Xinyuan-LilyGO/LilyGo-T-SIM7080G/examples/ModemFileUploadExample/image.png

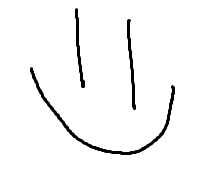
examples/ModemFileUploadExample/image.png
