Xinyuan-LilyGO/LilyGo-T-SIM7080G/examples/LoRaShield_LoRaTransmit/LoRaShield_LoRaTransmit.ino

/*
  RadioLib SX126x Transmit with Interrupts Example

  This example transmits LoRa packets with one second delays
  between them. Each packet contains up to 256 bytes
  of data, in the form of:
  - Arduino String
  - null-terminated char array (C-string)
  - arbitrary binary data (byte array)

  Other modules from SX126x family can also be used.

  For default module settings, see the wiki page
  https://github.com/jgromes/RadioLib/wiki/Default-configuration#sx126x---lora-modem

  For full API reference, see the GitHub Pages
  https://jgromes.github.io/RadioLib/
*/

//  * @note      This example is only available for SimShield

// include the library
#include <RadioLib.h>

#define SIMSHIELD_MOSI                      (11)
#define SIMSHIELD_MISO                      (13)
#define SIMSHIELD_SCK                       (12)
#define SIMSHIELD_SD_CS                     (21)
#define SIMSHIELD_RADIO_BUSY                (48)
#define SIMSHIELD_RADIO_CS                  (45)
#define SIMSHIELD_RADIO_IRQ                 (8)
#define SIMSHIELD_RADIO_RST                 (47)

SX1262 radio = new Module(SIMSHIELD_RADIO_CS, SIMSHIELD_RADIO_IRQ, SIMSHIELD_RADIO_RST, SIMSHIELD_RADIO_BUSY);

// save transmission state between loops
int transmissionState = RADIOLIB_ERR_NONE;

// flag to indicate that a packet was sent
volatile bool transmittedFlag = false;

// this function is called when a complete packet
// is transmitted by the module
// IMPORTANT: this function MUST be 'void' type
//            and MUST NOT have any arguments!
ICACHE_RAM_ATTR void setFlag(void)
{
    // we sent a packet, set the flag
    transmittedFlag = true;
}

void setup()
{
    Serial.begin(115200);

    //Pull spi devices cs to high
    pinMode(SIMSHIELD_SD_CS, OUTPUT);
    pinMode(SIMSHIELD_RADIO_CS, OUTPUT);

    digitalWrite(SIMSHIELD_SD_CS, HIGH);
    digitalWrite(SIMSHIELD_RADIO_CS, HIGH);

    SPI.begin(SIMSHIELD_SCK, SIMSHIELD_MISO, SIMSHIELD_MOSI);

    // initialize SX1262 with default settings
    Serial.print(F("[SX1262] Initializing ... "));
    int state = radio.begin(868.0);
    if (state == RADIOLIB_ERR_NONE) {
        Serial.println(F("success!"));
    } else {
        Serial.print(F("failed, code "));
        Serial.println(state);
        while (true) {
            delay(10);
        }
    }

    // set the function that will be called
    // when packet transmission is finished
    radio.setPacketSentAction(setFlag);

    // start transmitting the first packet
    Serial.print(F("[SX1262] Sending first packet ... "));

    // you can transmit C-string or Arduino string up to
    // 256 characters long
    transmissionState = radio.startTransmit("Hello World!");

    // you can also transmit byte array up to 256 bytes long
    /*
      byte byteArr[] = {0x01, 0x23, 0x45, 0x67,
                        0x89, 0xAB, 0xCD, 0xEF};
      state = radio.startTransmit(byteArr, 8);
    */
}

// counter to keep track of transmitted packets
int count = 0;

void loop()
{
    // check if the previous transmission finished
    if (transmittedFlag) {
        // reset flag
        transmittedFlag = false;

        if (transmissionState == RADIOLIB_ERR_NONE) {
            // packet was successfully sent
            Serial.println(F("transmission finished!"));

            // NOTE: when using interrupt-driven transmit method,
            //       it is not possible to automatically measure
            //       transmission data rate using getDataRate()

        } else {
            Serial.print(F("failed, code "));
            Serial.println(transmissionState);

        }

        // clean up after transmission is finished
        // this will ensure transmitter is disabled,
        // RF switch is powered down etc.
        radio.finishTransmit();

        // wait a second before transmitting again
        delay(1000);

        // send another one
        Serial.print(F("[SX1262] Sending another packet ... "));

        // you can transmit C-string or Arduino string up to
        // 256 characters long
        String str = "Hello World! #" + String(count++);
        transmissionState = radio.startTransmit(str);

        // you can also transmit byte array up to 256 bytes long
        /*
          byte byteArr[] = {0x01, 0x23, 0x45, 0x67,
                            0x89, 0xAB, 0xCD, 0xEF};
          transmissionState = radio.startTransmit(byteArr, 8);
        */
    }
}
